Blazecool789/WRO-2025-Oaklabs/Bot Photos/Back View.jpg

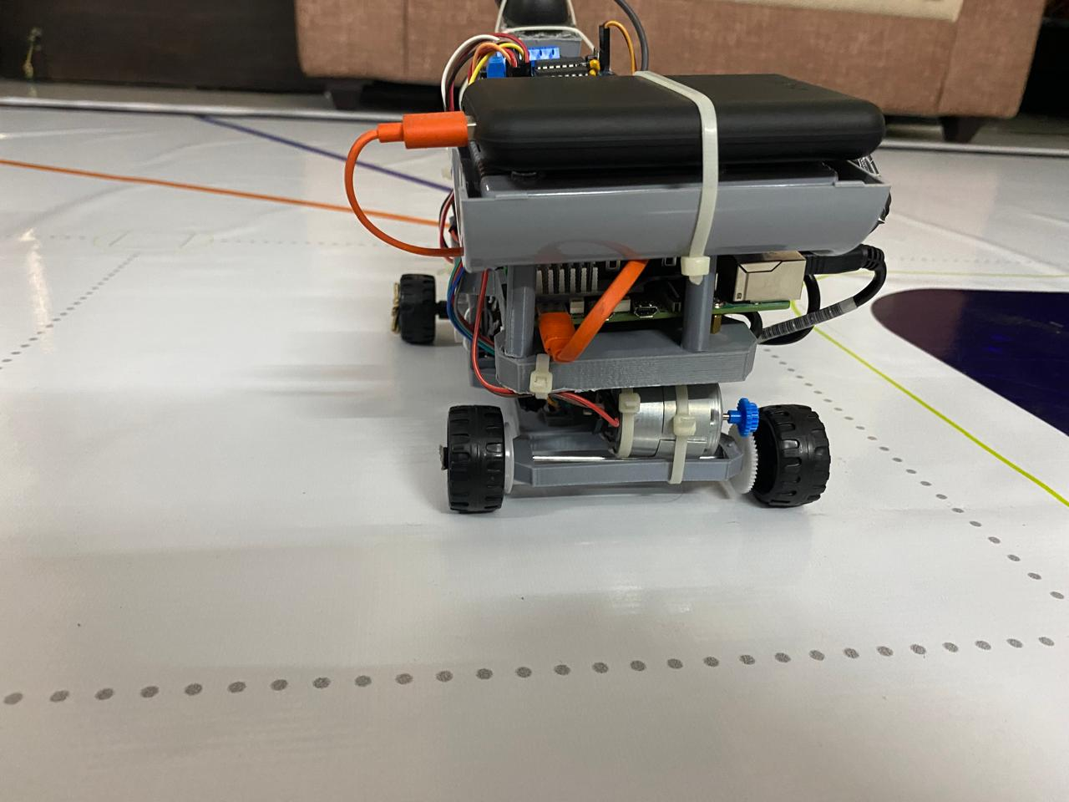
Bot Photos/Back View.jpg
