Blazecool789/WRO-2025-Oaklabs/Diagrams and Schemes/Circuit diagram .jpg

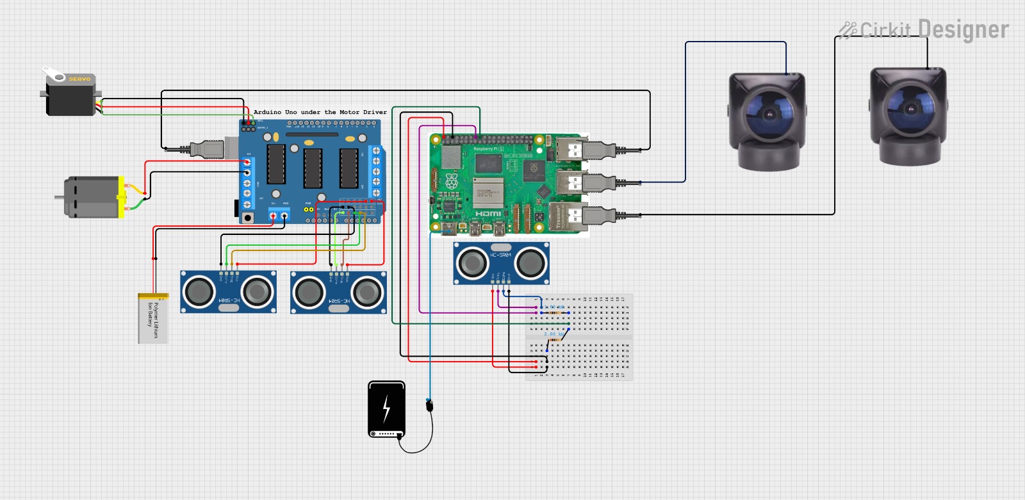
Diagrams and Schemes/Circuit diagram .jpg
