Blazecool789/WRO-2025-Oaklabs/3D designs/Steering Actuator/Steering Actuator v6.3mf

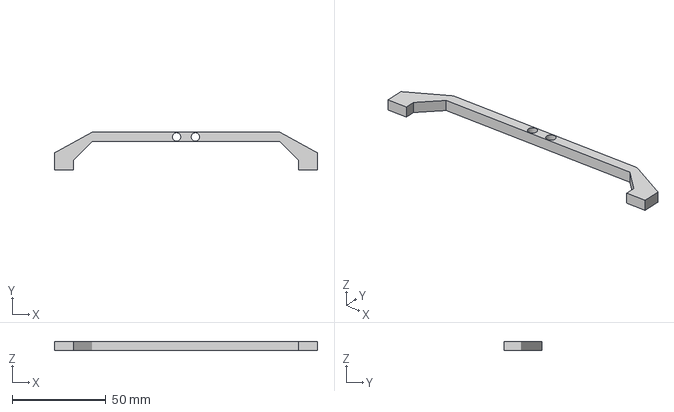
[picture p26: CAD file, 2025-07-22, an earlier design]
3D designs/Steering Actuator/Steering Actuator v6.3mf
140.0 x 20.0 x 5.00 mm
