Blazecool789/WRO-2025-Oaklabs/3D designs/Gear/Back Gear v1.3mf

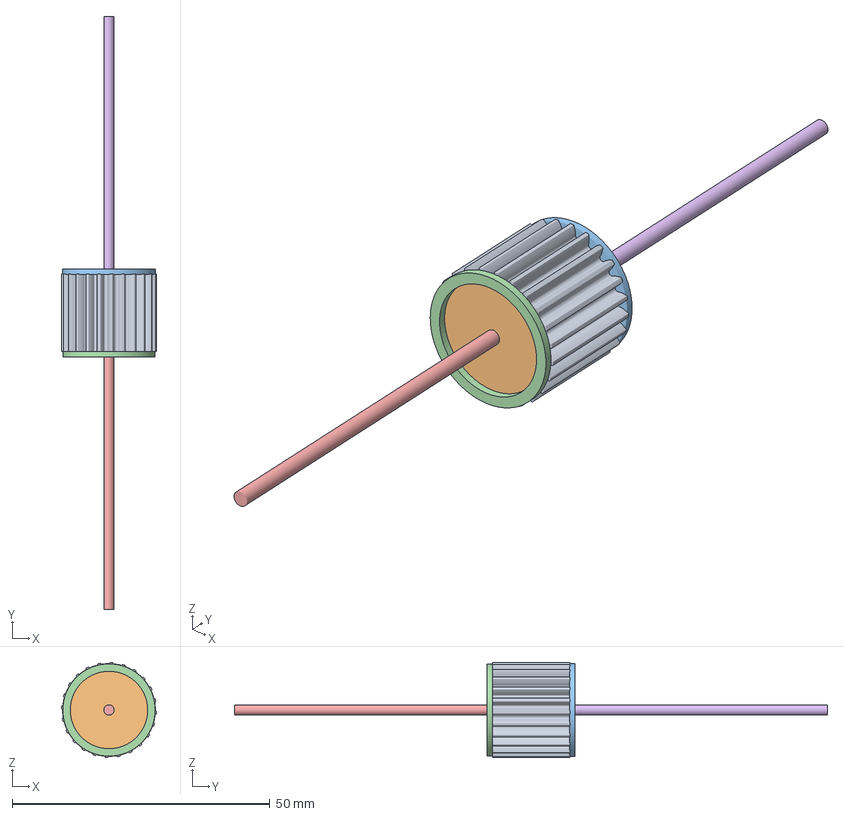
[picture p27: CAD file, 2025-07-22, an earlier design]
3D designs/Gear/Back Gear v1.3mf
18.5 x 115.0 x 18.5 mm
